dremeier/Arduino-JK-BMS-To-Pylontech-CAN-PCB/PICs/IMG_6281.JPG

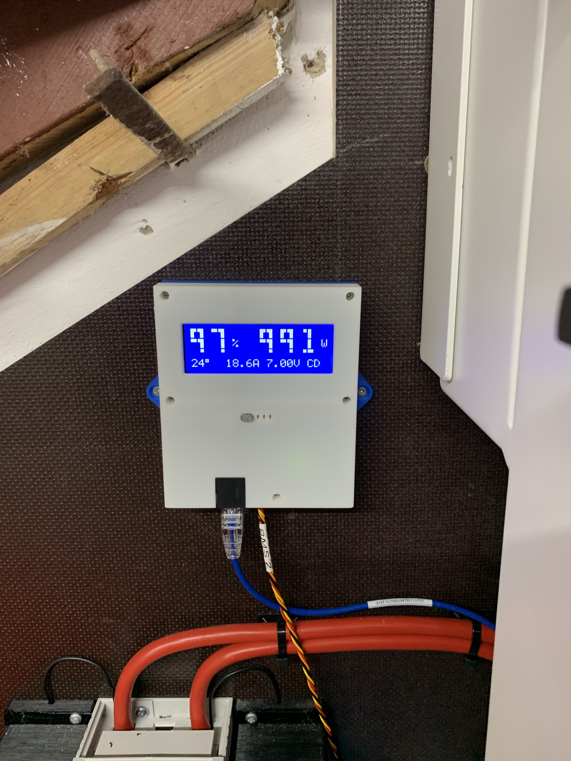
PICs/IMG_6281.JPG
