dremeier/Arduino-JK-BMS-To-Pylontech-CAN-PCB/PICs/IMG_6276.JPG

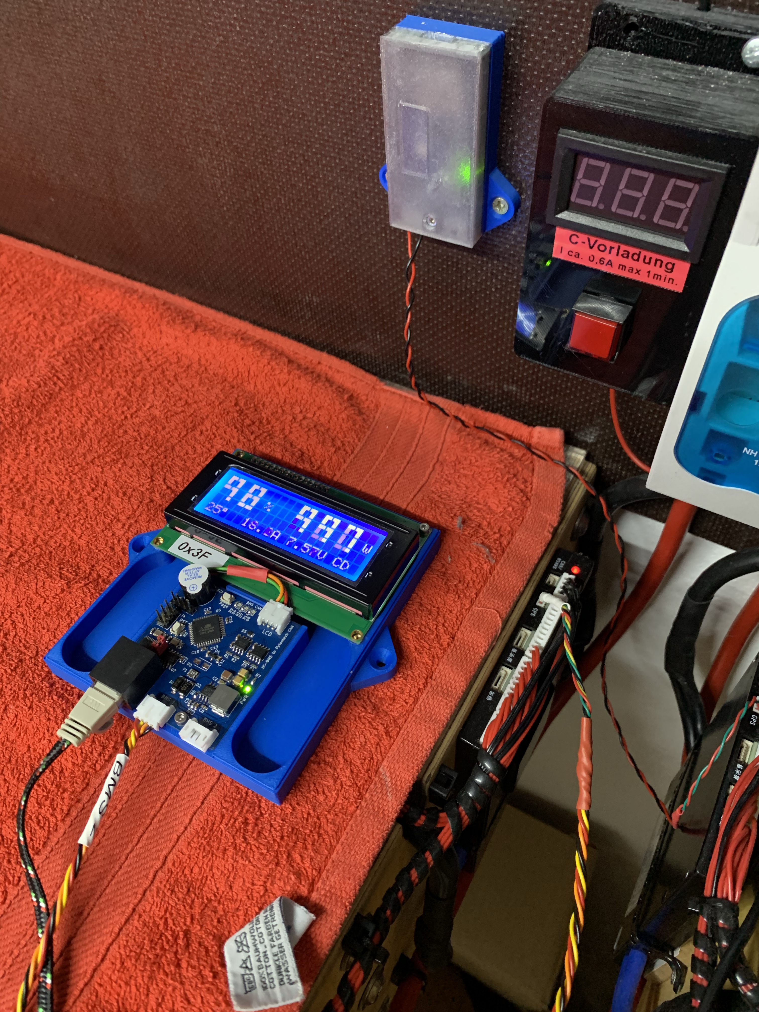
PICs/IMG_6276.JPG
